pendor/SV01-BIQU-H2/images/blockers-back.jpg

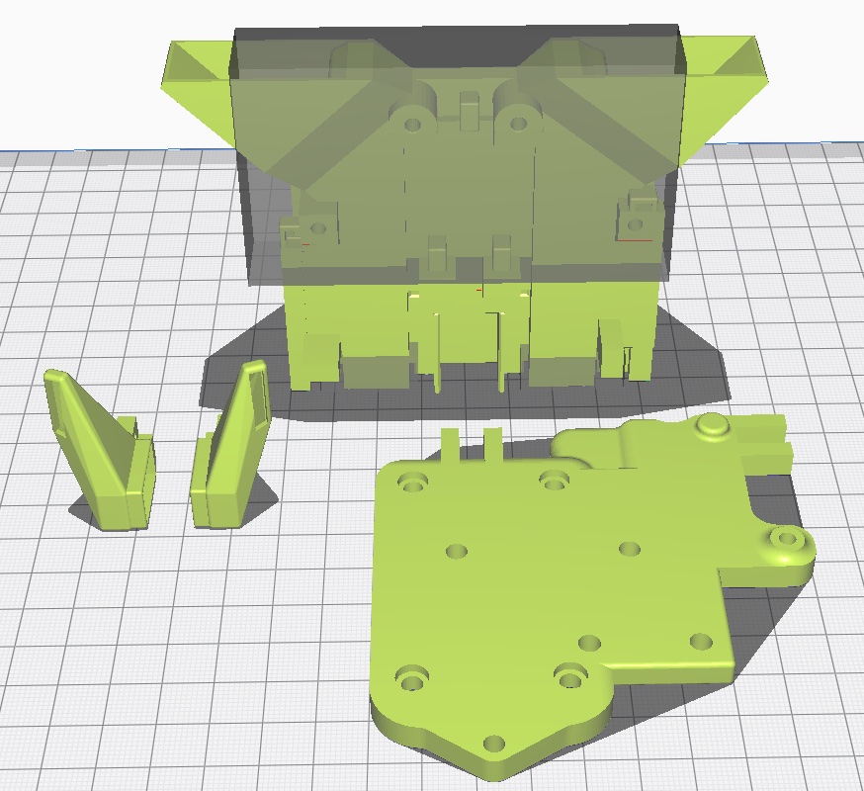
images/blockers-back.jpg
