pendor/SV01-BIQU-H2/images/blockers-front.jpg

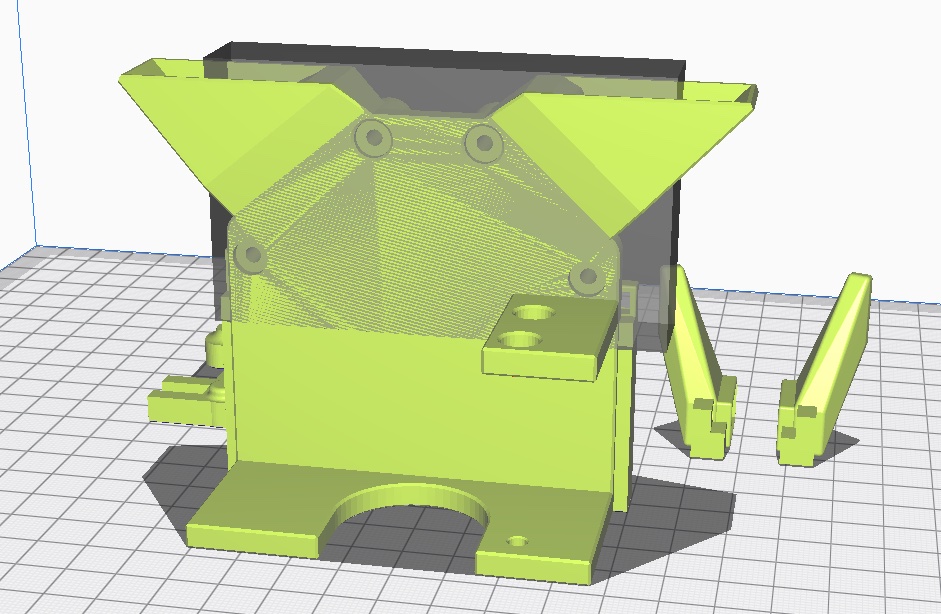
images/blockers-front.jpg
