pendor/SV01-BIQU-H2/images/supports.jpg

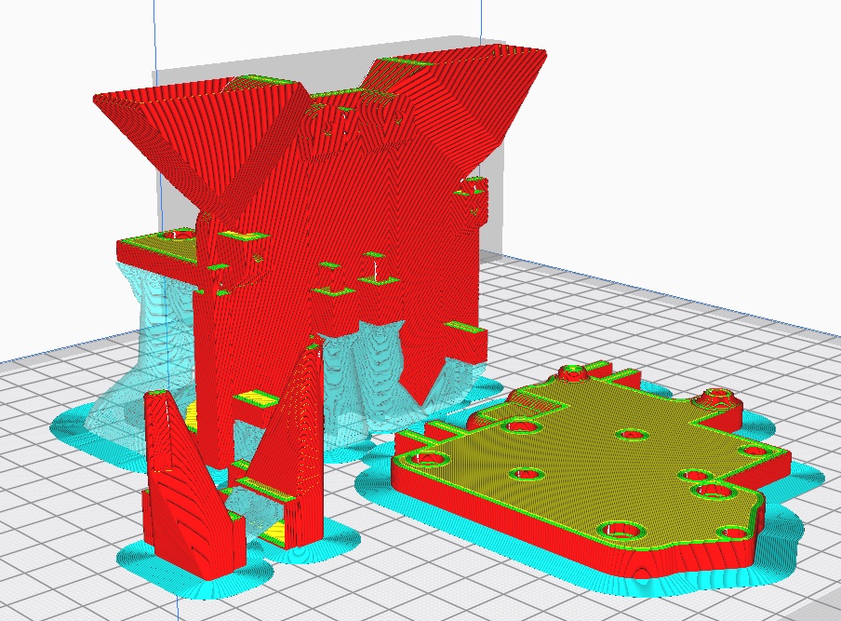
images/supports.jpg
