pendor/SV01-BIQU-H2/originals/Ender 6 - BIQU H2 Extruder/images/BIQU_H2_Halterung.png

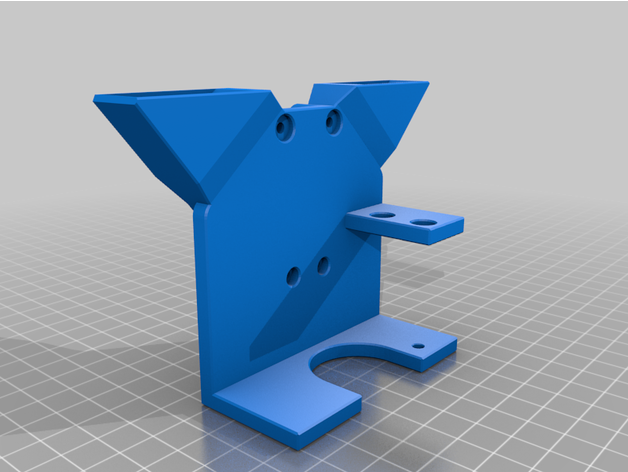
originals/Ender 6 - BIQU H2 Extruder/images/BIQU_H2_Halterung.png
