pendor/SV01-BIQU-H2/originals/Ender 6 - BIQU H2 Extruder/images/CableChainDock.png

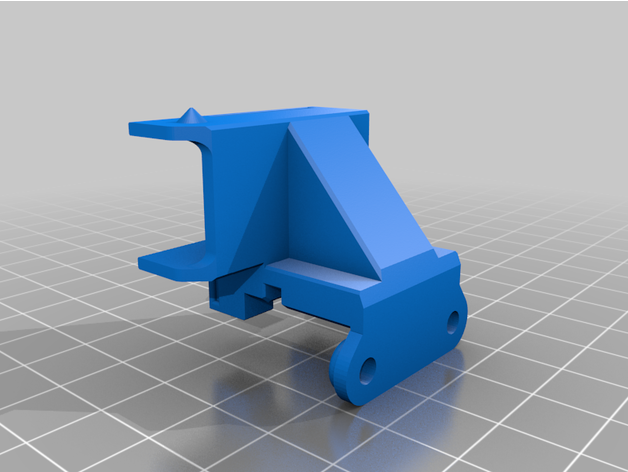
originals/Ender 6 - BIQU H2 Extruder/images/CableChainDock.png
