pendor/SV01-BIQU-H2/imports/h2model/Biqu_H2.STEP

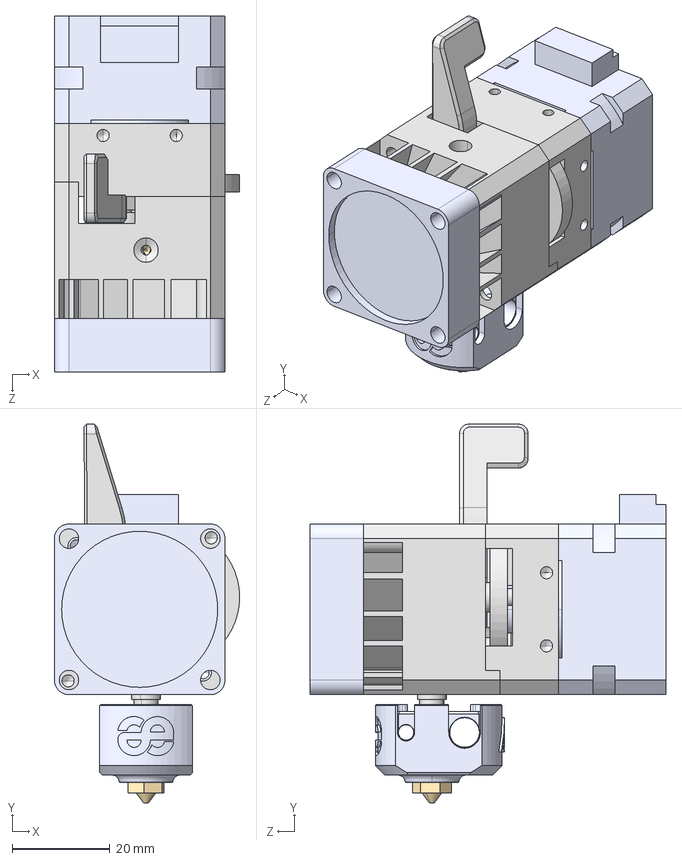
[picture p26: CAD file, 2021-09-14]
imports/h2model/Biqu_H2.STEP
38.0 x 77.7 x 73.0 mm
Biqu_H2_Heatsink
Biqu_H2_Interface_Moteur
Biqu_H2_Motor
Axe_Bras
Biqu_H2_Bras
Arm_Gear
Gear_1
Gear_2
E3D V6 Nozzle 0.4mm
Phaetus_HB
HeatBreak
Silicone_Sock
3511_Fan
