pendor/SV01-BIQU-H2/originals/Ender 6 - BIQU H2 Extruder/files/HotendLüfterAdapter_-_40x40.stl

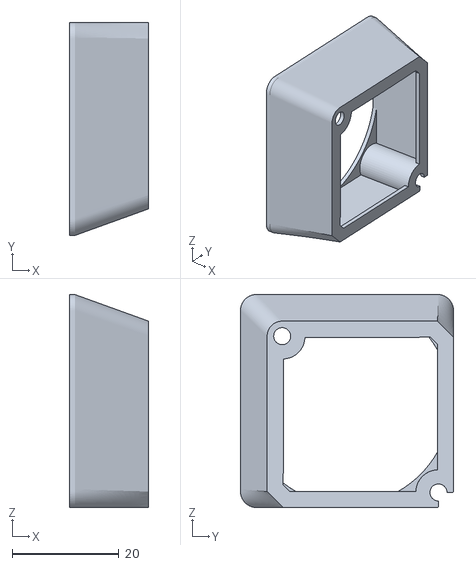
[picture p27: CAD file, 2022-01-02]
originals/Ender 6 - BIQU H2 Extruder/files/HotendLüfterAdapter_-_40x40.stl
14.9 x 40.0 x 40.0
