pendor/SV01-BIQU-H2/imports/h2model/Biqu_H2_-_Biqu_H2_Bras-1.STL

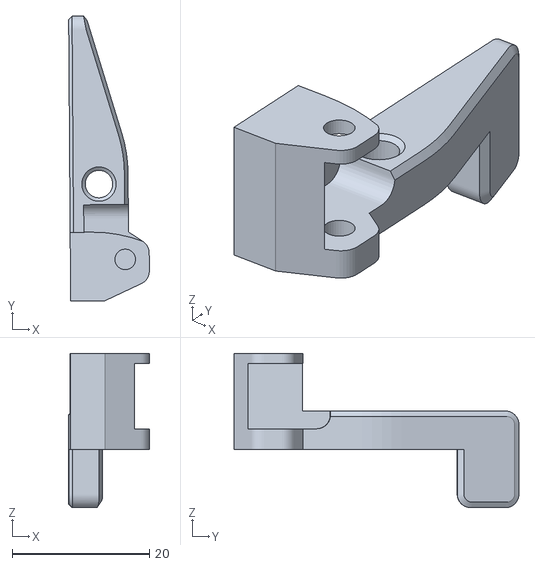
[picture p28: CAD file, 2021-09-14]
imports/h2model/Biqu_H2_-_Biqu_H2_Bras-1.STL
11.8 x 41.5 x 22.5
