pendor/SV01-BIQU-H2/originals/Ender 6 - BIQU H2 Extruder/files/CableChainDock.stl

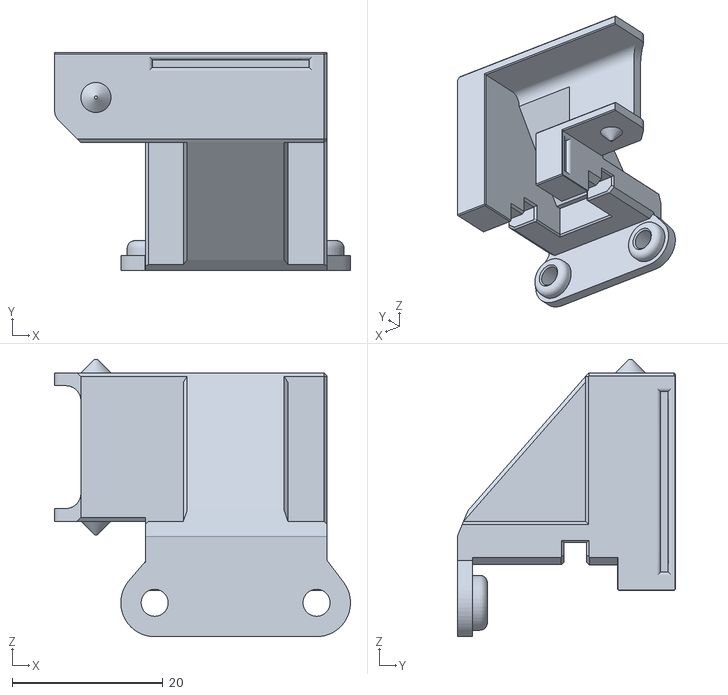
[picture p29: CAD file, 2022-01-02]
originals/Ender 6 - BIQU H2 Extruder/files/CableChainDock.stl
39.3 x 29.0 x 36.8
