pendor/SV01-BIQU-H2/imports/h2model/Biqu_H2_-_E3D_V6_Nozzle_0.4mm-1.STL

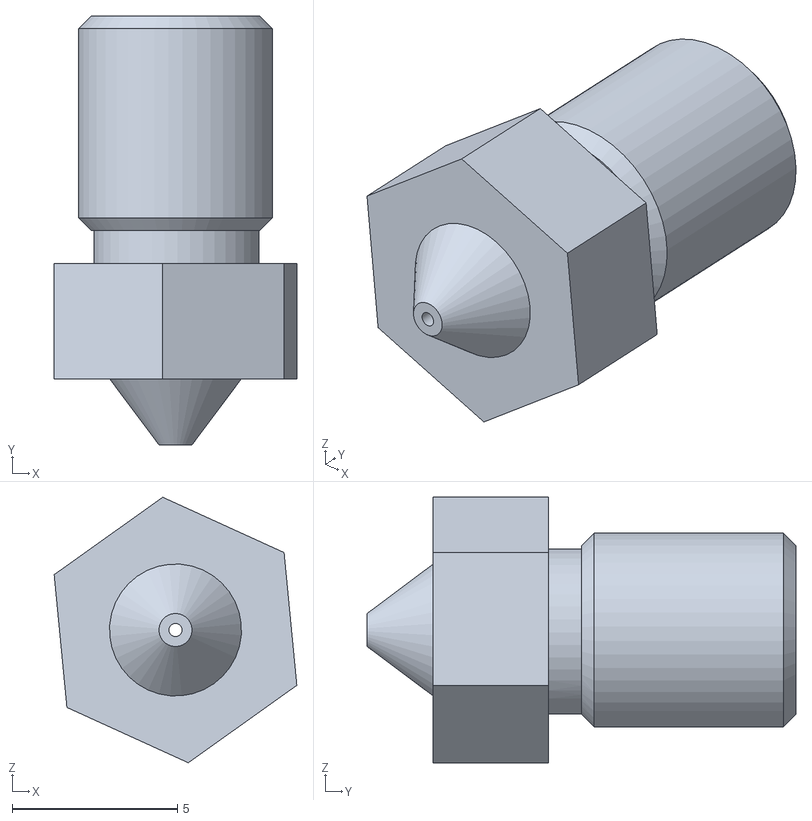
[picture p30: CAD file, 2021-09-14]
imports/h2model/Biqu_H2_-_E3D_V6_Nozzle_0.4mm-1.STL
7.35 x 13.0 x 8.05
