pendor/SV01-BIQU-H2/originals/Ender 6 - BIQU H2 Extruder/files/Luft_Düse_Links.stl

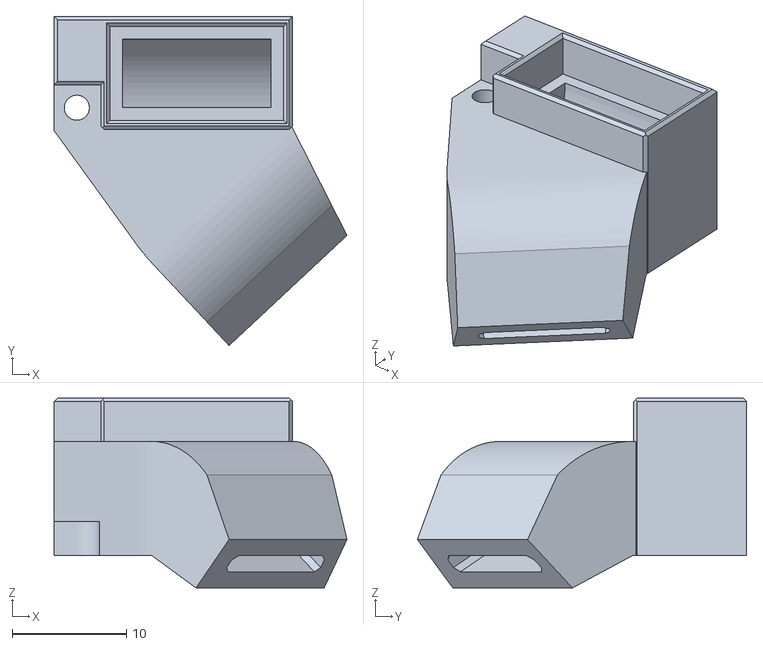
[picture p31: CAD file, 2021-09-14]
originals/Ender 6 - BIQU H2 Extruder/files/Luft_Düse_Links.stl
25.7 x 28.8 x 16.6
