pendor/SV01-BIQU-H2/imports/h2model/Biqu_H2_-_Biqu_H2_Motor-1.STL

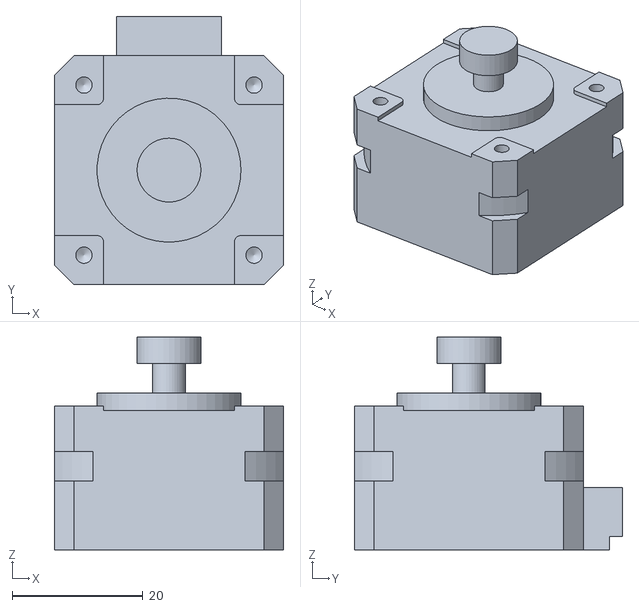
[picture p32: CAD file, 2021-09-14]
imports/h2model/Biqu_H2_-_Biqu_H2_Motor-1.STL
35.0 x 41.0 x 32.5
