pendor/SV01-BIQU-H2/originals/Ender 6 - BIQU H2 Extruder/files/Luft_Düse_Rechts.stl

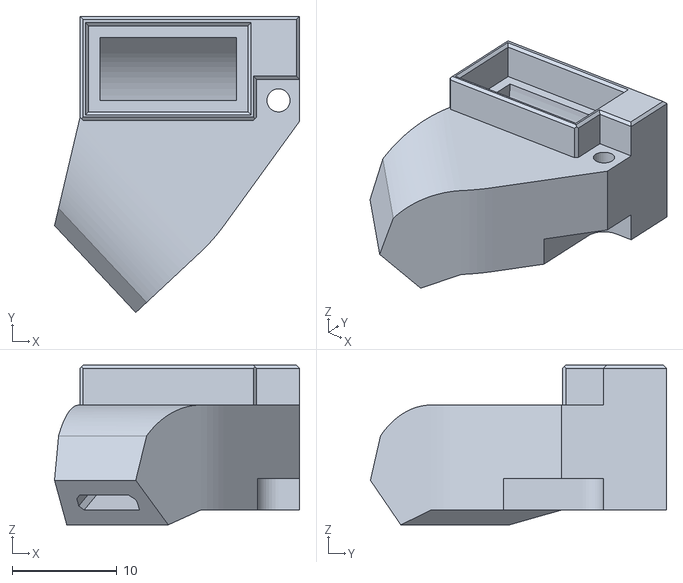
[picture p33: CAD file, 2021-09-14]
originals/Ender 6 - BIQU H2 Extruder/files/Luft_Düse_Rechts.stl
23.3 x 28.2 x 15.2
