pendor/SV01-BIQU-H2/imports/h2model/Biqu_H2_-_Biqu_H2_Heatsink-1.STL

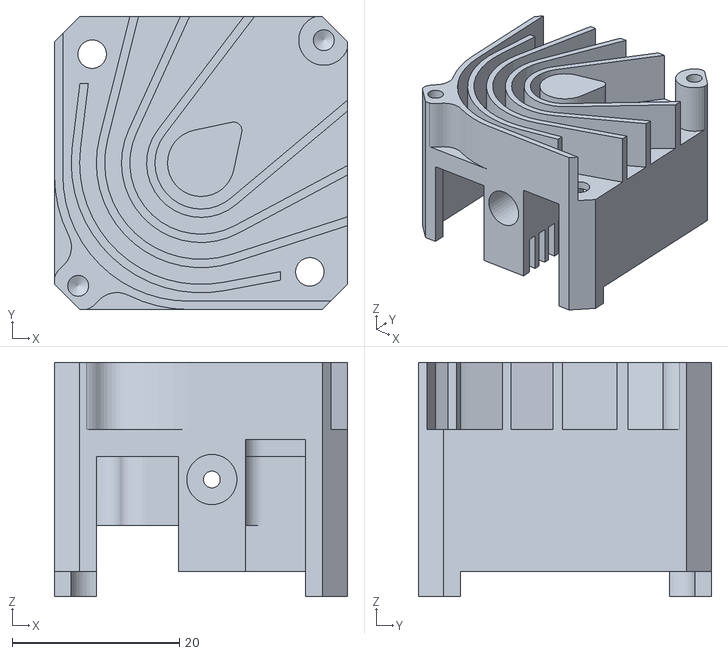
[picture p34: CAD file, 2021-09-14]
imports/h2model/Biqu_H2_-_Biqu_H2_Heatsink-1.STL
35.0 x 35.0 x 28.0
