pendor/SV01-BIQU-H2/imports/h2model/Biqu_H2_-_Arm_Gear-1.STL

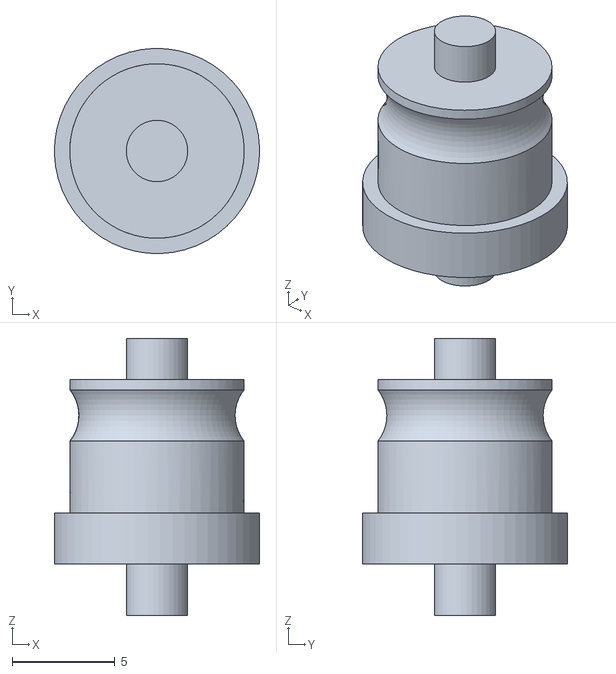
[picture p35: CAD file, 2021-09-14]
imports/h2model/Biqu_H2_-_Arm_Gear-1.STL
10.00 x 10.00 x 13.5
