pendor/SV01-BIQU-H2/imports/h2model/Biqu_H2_-_Gear_2-1.STL

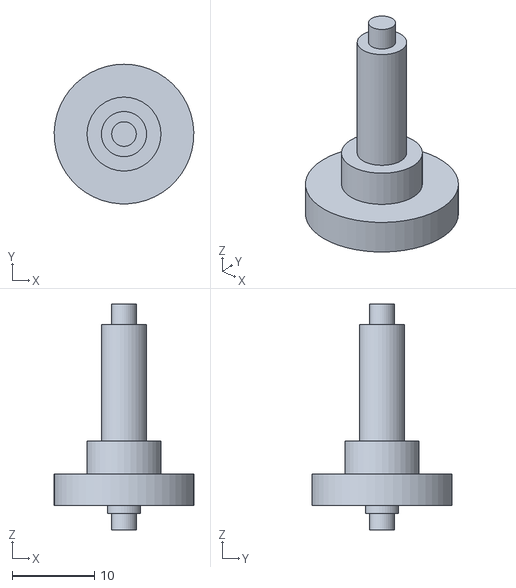
[picture p36: CAD file, 2021-09-14]
imports/h2model/Biqu_H2_-_Gear_2-1.STL
17.0 x 17.0 x 27.5
