pendor/SV01-BIQU-H2/imports/h2model/Biqu_H2_-_HeatBreak-1.STL

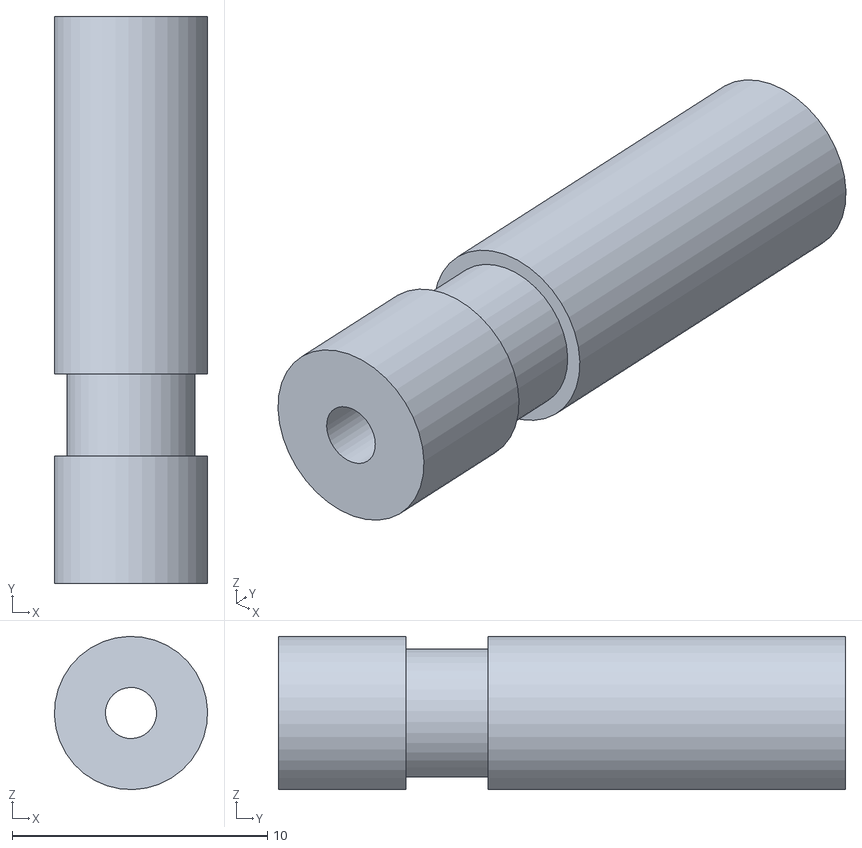
[picture p37: CAD file, 2021-09-14]
imports/h2model/Biqu_H2_-_HeatBreak-1.STL
6.00 x 22.2 x 6.00
