pendor/SV01-BIQU-H2/imports/h2model/Biqu_H2_-_Silicone_Sock-1.STL

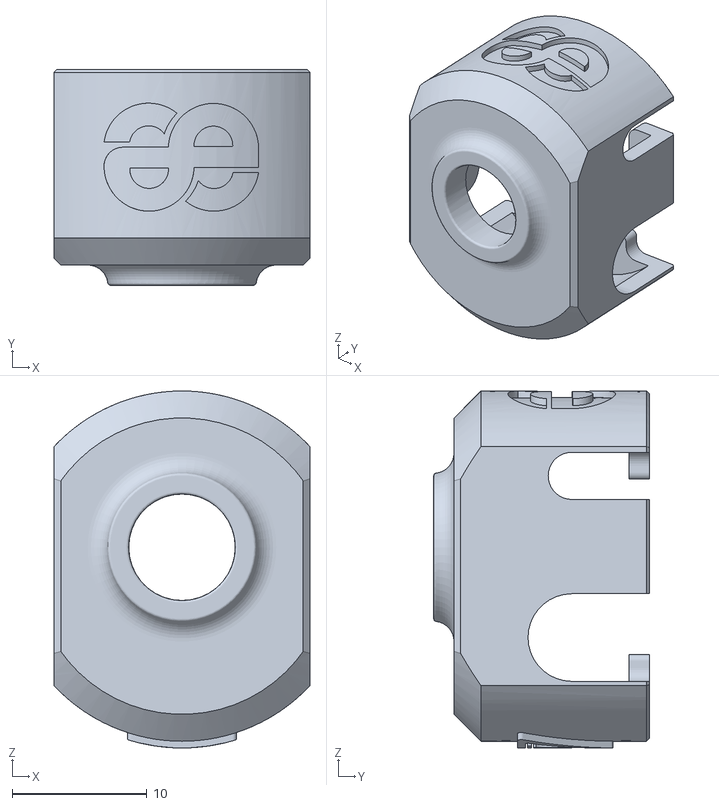
[picture p38: CAD file, 2021-09-14]
imports/h2model/Biqu_H2_-_Silicone_Sock-1.STL
19.0 x 16.0 x 26.5
