pendor/SV01-BIQU-H2/imports/h2model/Biqu_H2_-_Gear_1-1.STL

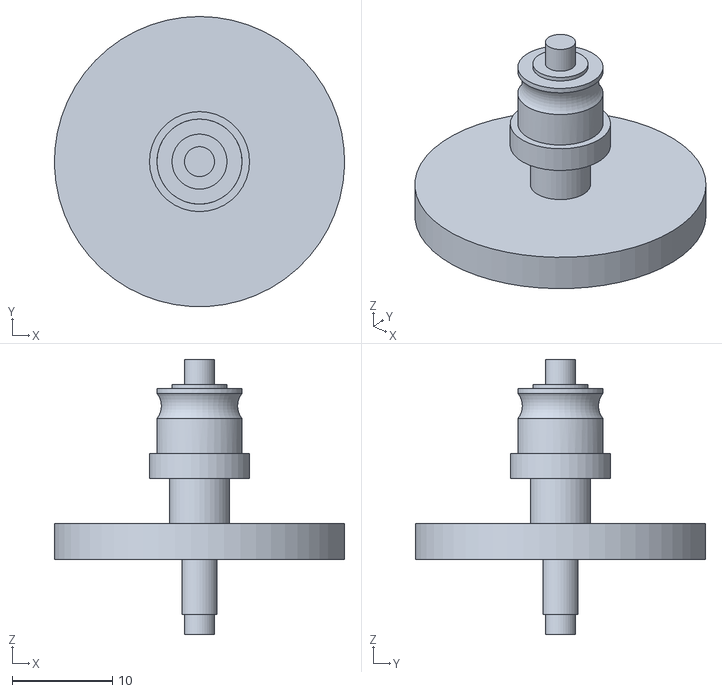
[picture p39: CAD file, 2021-09-14]
imports/h2model/Biqu_H2_-_Gear_1-1.STL
29.0 x 29.0 x 27.5
